secures92/CADMouse/Media/pics/version 0.2/01-03-2014 14-36-56.png

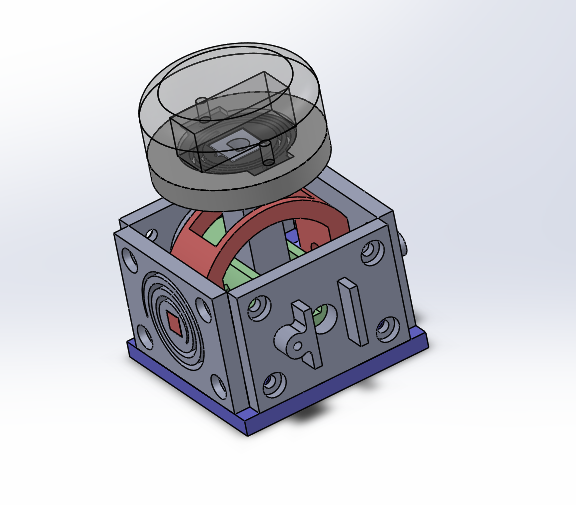
Media/pics/version 0.2/01-03-2014 14-36-56.png
