secures92/CADMouse/Media/pics/version 0.2/2014-02-24 00.38.54.jpg

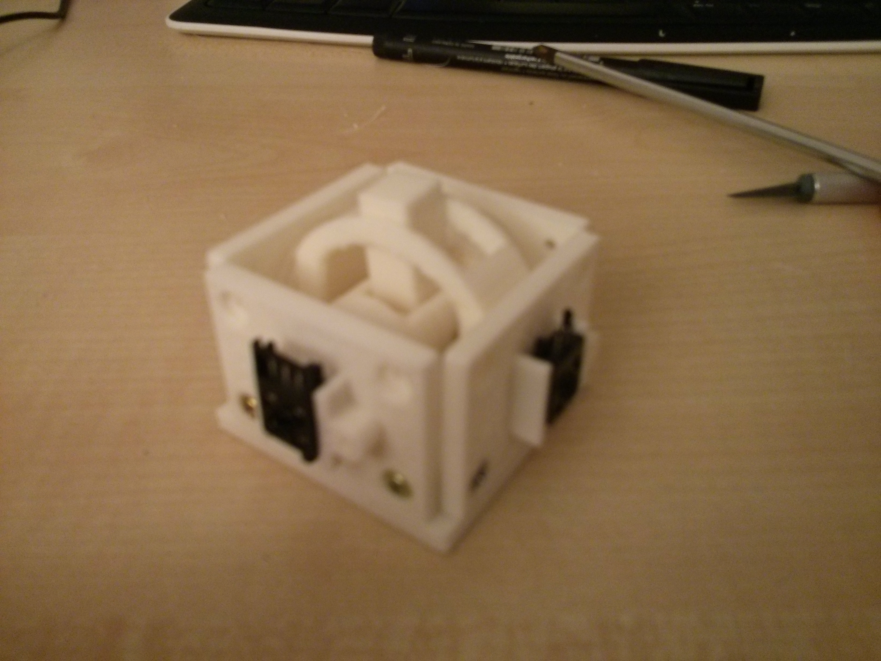
Media/pics/version 0.2/2014-02-24 00.38.54.jpg
