secures92/CADMouse/SolidWorks/Version 0.2/spring_wall.SLDPRT

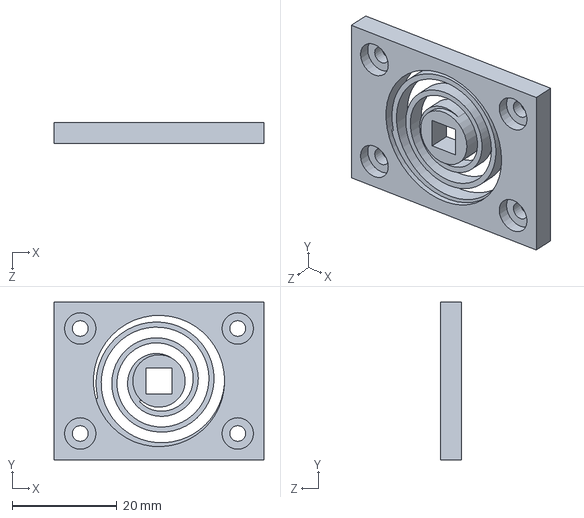
[picture p24: CAD file, 2014-03-01, an earlier design]
SolidWorks/Version 0.2/spring_wall.SLDPRT
40.0 x 30.0 x 4.00 mm
