secures92/CADMouse/SolidWorks/Version 0.1/connector.SLDPRT

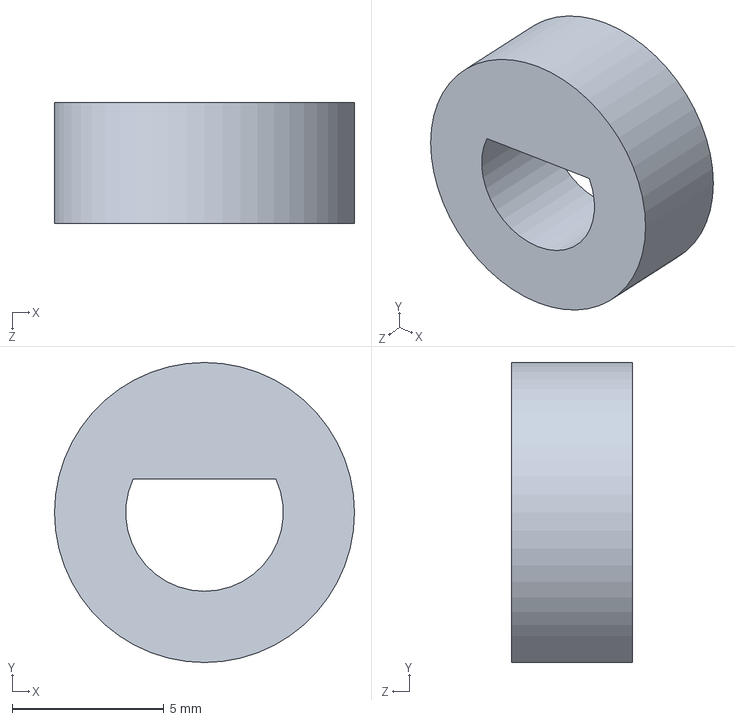
[picture p25: CAD file, 2014-03-01, an earlier design]
SolidWorks/Version 0.1/connector.SLDPRT
9.90 x 9.90 x 4.00 mm
